mattwach/matrix_clock/src/clock_render.h

#ifndef CLOCK_RENDER_H
#define CLOCK_RENDER_H

#include <inttypes.h>
#include "clock_settings.h"

#if defined(led_matrix_64x32)
  #define MATRIX_ONLY_MODE_INDEX 1
#endif

// provides a common interface for rendering a clock
uint8_t clock_render(
  uint32_t* led,
  uint8_t button_pressed,
  uint32_t frame_index,
  uint16_t time_hhmm,
  const struct ClockSettings* settings);

// returns the number of available display modes
uint8_t clock_render_num_display_modes(void);
// maps a display mode index to a name.
const char* clock_render_display_mode_name(uint8_t mode);
// change current display mode
void clock_render_set_display_mode(uint8_t mode);
uint8_t clock_render_get_display_mode(void);
void clock_render_reset_mode_change(void);
// returns the next mode change time in hhmm
uint16_t clock_render_next_mode_change(void);

#endif
